mlab-modules/LED7SEG02/doc/gen/dxf/LED7SEG02-F_Courtyard.dxf

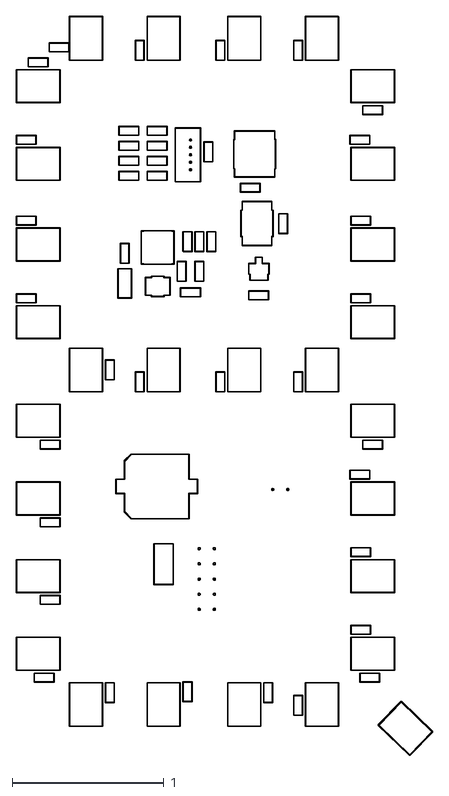
[picture p15: CAD file, 2026-02-07]
doc/gen/dxf/LED7SEG02-F_Courtyard.dxf
2.75 x 4.87
