mlab-modules/LED7SEG02/doc/gen/dxf/LED7SEG02-F_Adhesive.dxf

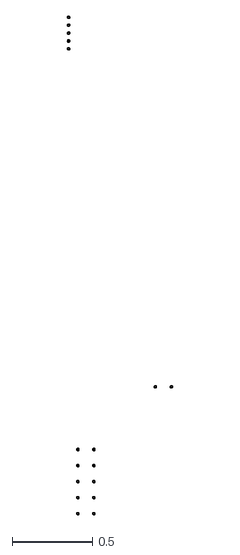
[picture p16: CAD file, 2026-02-07]
doc/gen/dxf/LED7SEG02-F_Adhesive.dxf
0.655 x 3.11
