mlab-modules/LED7SEG02/doc/gen/dxf/LED7SEG02-B_Fab.dxf

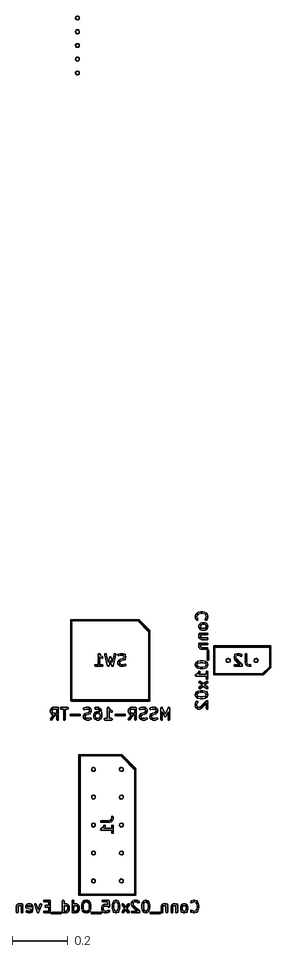
[picture p17: CAD file, 2026-02-07]
doc/gen/dxf/LED7SEG02-B_Fab.dxf
0.912 x 3.22
