mlab-modules/LED7SEG02/doc/gen/dxf/LED7SEG02-Edge_Cuts.dxf

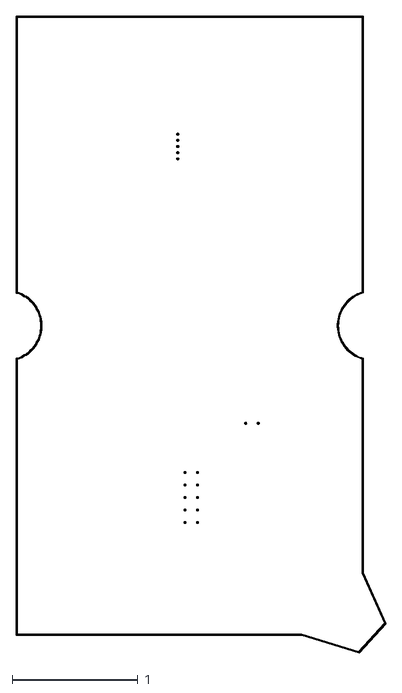
[picture p18: CAD file, 2026-02-07]
doc/gen/dxf/LED7SEG02-Edge_Cuts.dxf
2.94 x 5.07
